arkadiuszmakarenko/ReAmiga1200USBHID/firmware/src/User/gpio.c

#include "gpio.h"

void GPIO_Config() {
    // RCC_APB2Periph_GPIOA
    RCC_APB2PeriphClockCmd (RCC_APB2Periph_GPIOA, ENABLE);
    RCC_APB2PeriphClockCmd (RCC_APB2Periph_GPIOB, ENABLE);
    RCC_APB2PeriphClockCmd (RCC_APB2Periph_GPIOC, ENABLE);
    RCC_APB2PeriphClockCmd (RCC_APB2Periph_AFIO, ENABLE);

    GPIO_InitTypeDef GPIO_InitStructure = {0};
    EXTI_InitTypeDef EXTI_InitStructure = {0};
    NVIC_InitTypeDef NVIC_InitStructure = {0};


    /*Configure GPIO pin Output Level */
    GPIO_WriteBit (LED_GPIO_Port, LED_Pin, Bit_SET);
    GPIO_WriteBit (GPIOB, RHQ_Pin | LVQ_Pin | BH_Pin | FV_Pin, Bit_RESET);
    GPIO_WriteBit (GPIOB, LB_Pin | RB_Pin, Bit_SET);
    GPIO_WriteBit (GPIOA, KBD_DATA_Pin | KBD_CLOCK_Pin | KB_RESET_GPIO_Pin | K0_Pin | K1_Pin | IRQ7_Pin, Bit_SET);
    GPIO_InitStructure.GPIO_Pin = GPIO_Pin_0;
    GPIO_InitStructure.GPIO_Mode = GPIO_Mode_Out_PP;
    GPIO_InitStructure.GPIO_Speed = GPIO_Speed_50MHz;
    GPIO_Init (GPIOA, &GPIO_InitStructure);

    GPIO_InitStructure.GPIO_Pin = GPIO_Pin_0;
    GPIO_InitStructure.GPIO_Mode = GPIO_Mode_Out_PP;
    GPIO_InitStructure.GPIO_Speed = GPIO_Speed_50MHz;
    GPIO_Init (GPIOA, &GPIO_InitStructure);


    /*Configure GPIO pins : PCPin PCPin PCPin */
    GPIO_InitStructure.GPIO_Pin = LED_Pin;
    GPIO_InitStructure.GPIO_Mode = GPIO_Mode_Out_OD;
    GPIO_InitStructure.GPIO_Speed = GPIO_Speed_50MHz;
    GPIO_Init (LED_GPIO_Port, &GPIO_InitStructure);


    GPIO_InitStructure.GPIO_Pin = LB_Pin | RB_Pin | RHQ_Pin | LVQ_Pin | BH_Pin | FV_Pin;
    GPIO_InitStructure.GPIO_Mode = GPIO_Mode_Out_PP;
    GPIO_InitStructure.GPIO_Speed = GPIO_Speed_50MHz;
    GPIO_Init (GPIOB, &GPIO_InitStructure);


    GPIO_InitStructure.GPIO_Pin = KBD_DATA_Pin | KBD_CLOCK_Pin | KB_RESET_GPIO_Pin | IRQ7_Pin;
    GPIO_InitStructure.GPIO_Mode = GPIO_Mode_Out_OD;
    GPIO_InitStructure.GPIO_Speed = GPIO_Speed_50MHz;
    GPIO_Init (GPIOA, &GPIO_InitStructure);


    GPIO_InitStructure.GPIO_Pin = K0_Pin | K1_Pin;
    GPIO_InitStructure.GPIO_Mode = GPIO_Mode_Out_PP;
    GPIO_InitStructure.GPIO_Speed = GPIO_Speed_50MHz;
    GPIO_Init (GPIOA, &GPIO_InitStructure);


    RCC_APB2PeriphClockCmd (RCC_APB2Periph_AFIO, ENABLE);
    RCC_APB2PeriphClockCmd (RCC_APB2Periph_GPIOB, ENABLE);

    GPIO_InitStructure.GPIO_Pin = GPIO_Pin_3;
    GPIO_InitStructure.GPIO_Mode = GPIO_Mode_IPU;
    GPIO_Init (GPIOB, &GPIO_InitStructure);


    GPIO_EXTILineConfig (GPIO_PortSourceGPIOB, GPIO_PinSource3);
    EXTI_InitStructure.EXTI_Line = EXTI_Line3;
    EXTI_InitStructure.EXTI_Mode = EXTI_Mode_Interrupt;
    EXTI_InitStructure.EXTI_Trigger = EXTI_Trigger_Falling;
    EXTI_InitStructure.EXTI_LineCmd = ENABLE;
    EXTI_Init (&EXTI_InitStructure);

    NVIC_InitStructure.NVIC_IRQChannel = EXTI3_IRQn;
    NVIC_InitStructure.NVIC_IRQChannelPreemptionPriority = 1;
    NVIC_InitStructure.NVIC_IRQChannelSubPriority = 1;
    NVIC_InitStructure.NVIC_IRQChannelCmd = ENABLE;
    NVIC_Init (&NVIC_InitStructure);
}
