arkadiuszmakarenko/ReAmiga1200USBHID/firmware/src/User/ch32v20x_it.c

/********************************** (C) COPYRIGHT *******************************
 * File Name          : ch32v20x_it.c
 * Author             : WCH
 * Version            : V1.0.0
 * Date               : 2021/06/06
 * Description        : Main Interrupt Service Routines.
*********************************************************************************
* Copyright (c) 2021 Nanjing Qinheng Microelectronics Co., Ltd.
* Attention: This software (modified or not) and binary are used for 
* microcontroller manufactured by Nanjing Qinheng Microelectronics.
*******************************************************************************/
#include "ch32v20x_it.h"
#include "mouse.h"


void NMI_Handler(void) __attribute__((interrupt("WCH-Interrupt-fast")));
void HardFault_Handler(void) __attribute__((interrupt("WCH-Interrupt-fast")));
void EXTI3_IRQHandler(void) __attribute__((interrupt("WCH-Interrupt-fast")));
/*********************************************************************
 * @fn      NMI_Handler
 *
 * @brief   This function handles NMI exception.
 *
 * @return  none
 */
void NMI_Handler(void)
{
}

/*********************************************************************
 * @fn      HardFault_Handler
 *
 * @brief   This function handles Hard Fault exception.
 *
 * @return  none
 */
void HardFault_Handler(void)
{
  while (1)
  {
  }
}

void EXTI3_IRQHandler(void)
{
    if(EXTI_GetITStatus(EXTI_Line3) != RESET)
    {
        ProcessScrollIRQ();
        EXTI_ClearITPendingBit(EXTI_Line3); /* Clear Flag */
    }
}
